CASE-Lab/REACH-Hardware/CAD/InventorProject/Manufacturing/CNC_VacuumCleaner_Adapter.stl

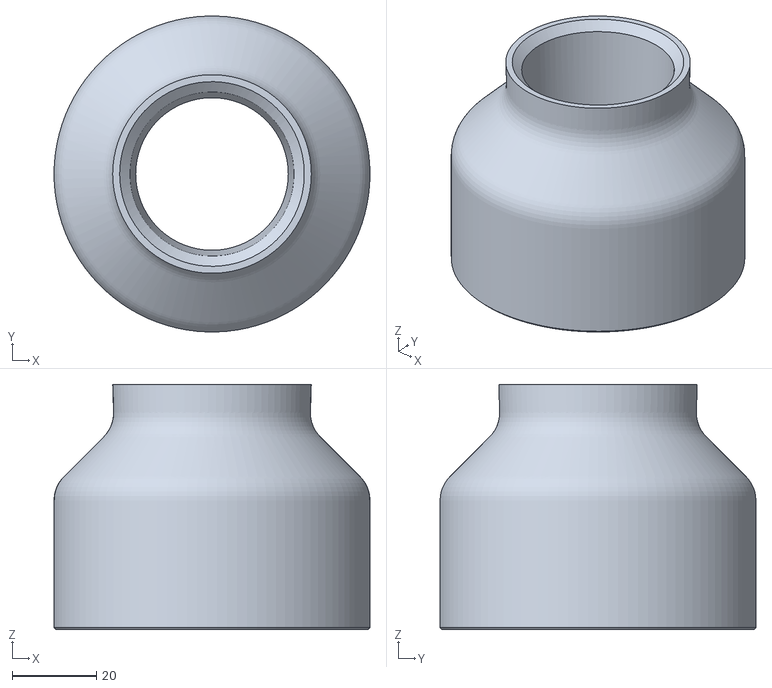
[picture p21: CAD file, 2021-09-06]
CAD/InventorProject/Manufacturing/CNC_VacuumCleaner_Adapter.stl
75.0 x 75.0 x 58.2
