CASE-Lab/REACH-Hardware/CAD/InventorProject/PCB_Outlines/ES_MODULE_OUTLINE.dxf

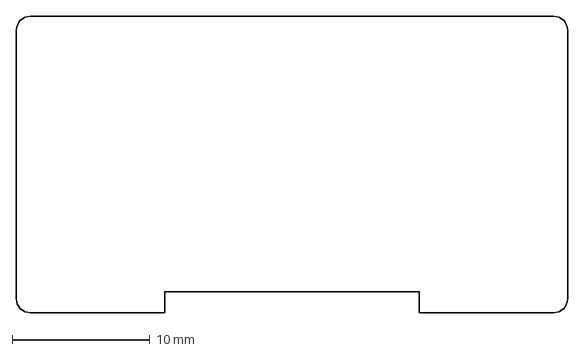
[picture p22: CAD file, 2021-09-06]
CAD/InventorProject/PCB_Outlines/ES_MODULE_OUTLINE.dxf
40.0 x 21.5 mm
