CASE-Lab/REACH-Hardware/CAD/InventorProject/Manufacturing/FrontText.dxf

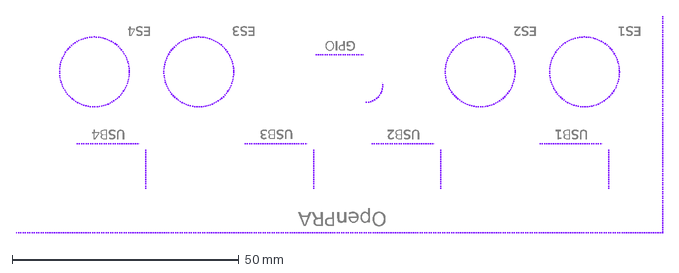
[picture p23: CAD file, 2021-09-06]
CAD/InventorProject/Manufacturing/FrontText.dxf
ES1
ES2
ES4
ES3
USB1
USB2
USB3
USB4
GPIO
OpenPRA
