CASE-Lab/REACH-Hardware/CAD/InventorProject/Manufacturing/UnicornPaneler/BackText.dxf

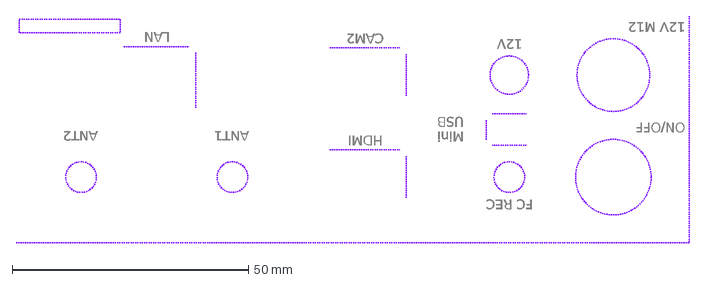
[picture p24: CAD file, 2021-09-06]
CAD/InventorProject/Manufacturing/UnicornPaneler/BackText.dxf
HDMI
CAM2
LAN
ANT1
12V
ANT2
Mini USB
FC REC
ON/OFF
12V M12
