CASE-Lab/REACH-Hardware/CAD/InventorProject/PCB_Outlines/FP_USB_OUTLINE.dxf

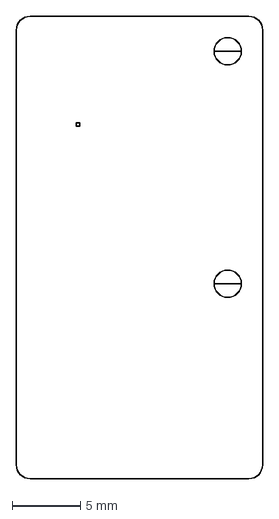
[picture p25: CAD file, 2021-09-06]
CAD/InventorProject/PCB_Outlines/FP_USB_OUTLINE.dxf
18.0 x 33.8 mm
