CASE-Lab/REACH-Hardware/CAD/InventorProject/Manufacturing/BottomTextThin.dxf

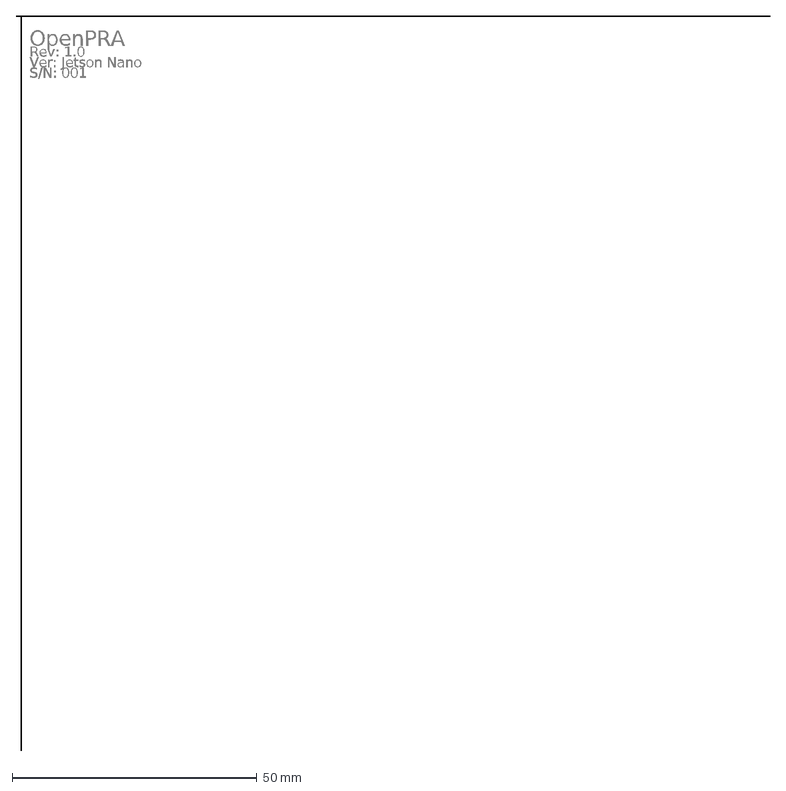
[picture p26: CAD file, 2021-09-06]
CAD/InventorProject/Manufacturing/BottomTextThin.dxf
OpenPRA Rev: 1.0 Ver: Jetson Nano S/N: 001
