CASE-Lab/REACH-Hardware/CAD/InventorProject/PCB_Outlines/FP_PCB_OUTLINE.dxf

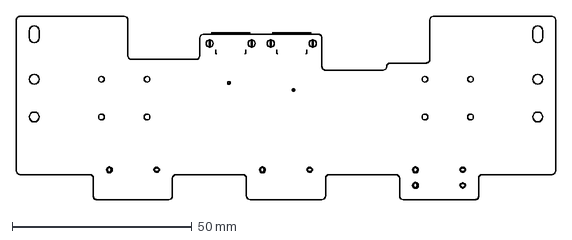
[picture p27: CAD file, 2021-09-06]
CAD/InventorProject/PCB_Outlines/FP_PCB_OUTLINE.dxf
150.0 x 51.0 mm
