CASE-Lab/REACH-Hardware/CAD/InventorProject/Manufacturing/Camera_Con_Spacer.stl

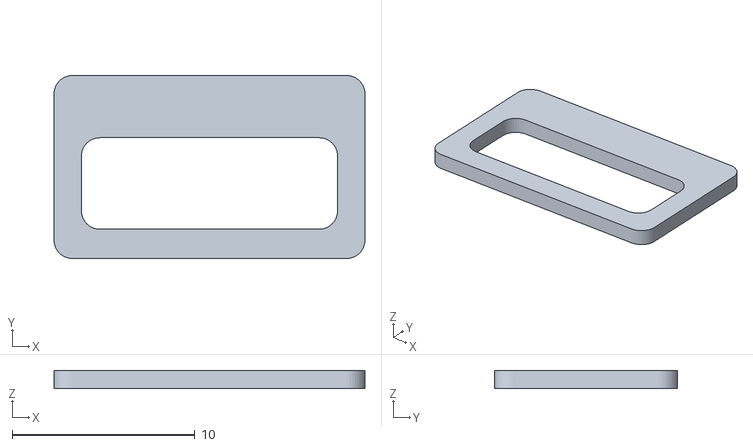
[picture p28: CAD file, 2021-09-06]
CAD/InventorProject/Manufacturing/Camera_Con_Spacer.stl
17.0 x 10.0 x 1.00
