CASE-Lab/REACH-Hardware/CAD/InventorProject/Manufacturing/UnicornPaneler/EngravingBackJig.dxf

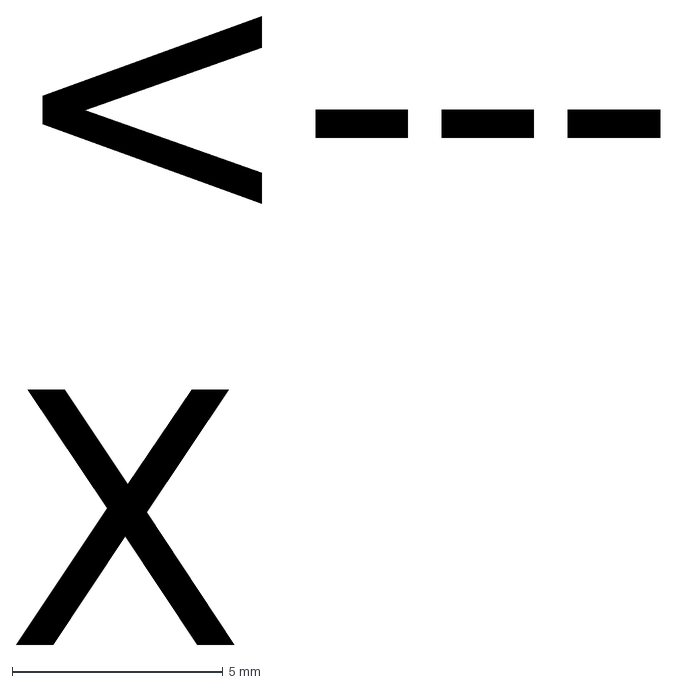
[picture p29: CAD file, 2021-09-06]
CAD/InventorProject/Manufacturing/UnicornPaneler/EngravingBackJig.dxf
<--- X
