CASE-Lab/REACH-Hardware/CAD/InventorProject/Manufacturing/UnicornPaneler/FrontText_V3_LOGO.dxf

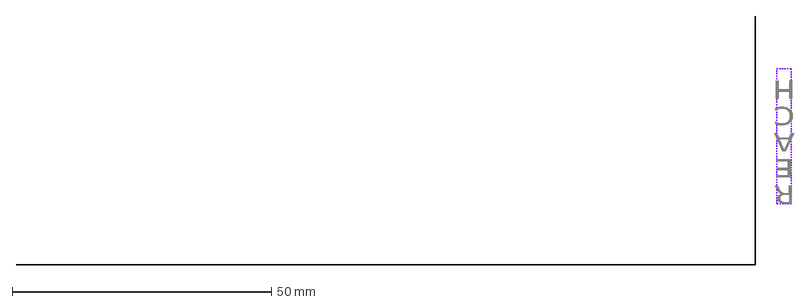
[picture p30: CAD file, 2021-09-06]
CAD/InventorProject/Manufacturing/UnicornPaneler/FrontText_V3_LOGO.dxf
R E A C H
