CASE-Lab/REACH-Hardware/CAD/InventorProject/Manufacturing/UnicornPaneler/BottomText.dxf

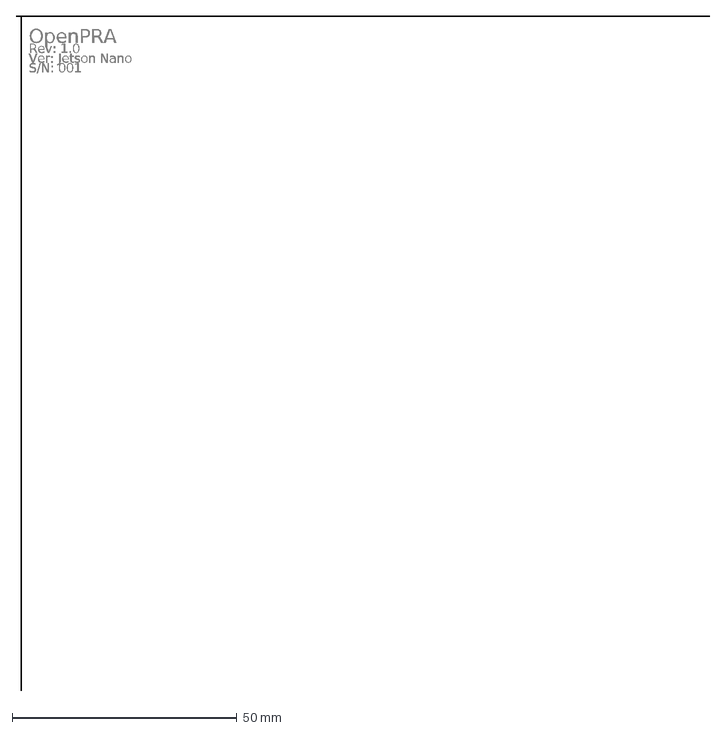
[picture p31: CAD file, 2021-09-06]
CAD/InventorProject/Manufacturing/UnicornPaneler/BottomText.dxf
OpenPRA Rev: 1.0 Ver: Jetson Nano S/N: 001
