CASE-Lab/REACH-Hardware/CAD/InventorProject/Manufacturing/test.dxf

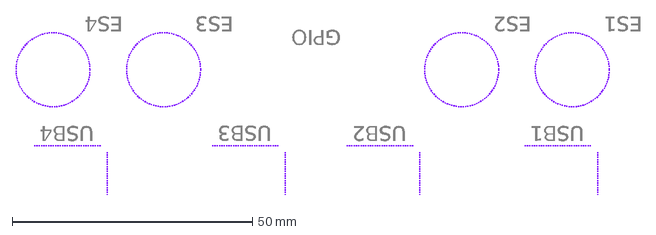
[picture p32: CAD file, 2021-09-06]
CAD/InventorProject/Manufacturing/test.dxf
ES1
ES2
ES4
ES3
USB1
USB2
USB3
USB4
GPIO
