CASE-Lab/REACH-Hardware/CAD/InventorProject/Manufacturing/Connector_Stop.stl

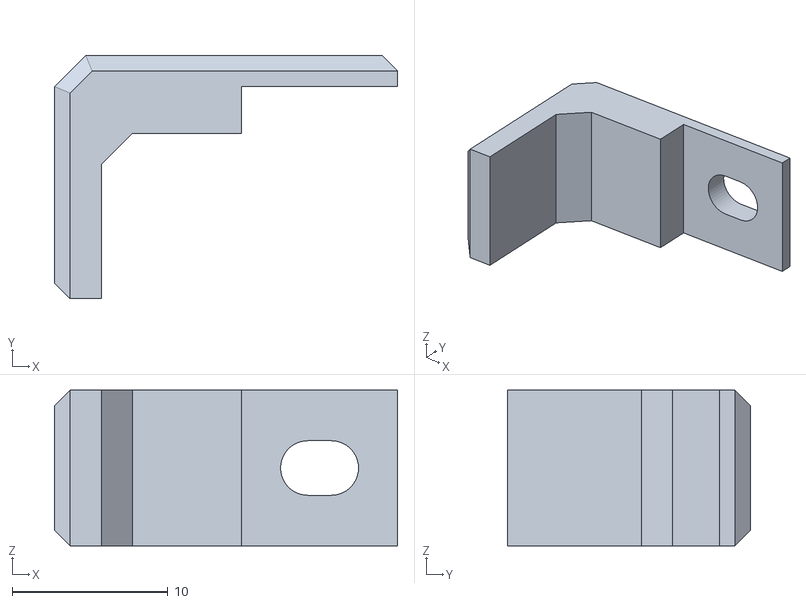
[picture p33: CAD file, 2021-09-06]
CAD/InventorProject/Manufacturing/Connector_Stop.stl
22.0 x 15.6 x 10.0
