CASE-Lab/REACH-Hardware/CAD/InventorProject/Manufacturing/TOP_Marking_ACU.dxf

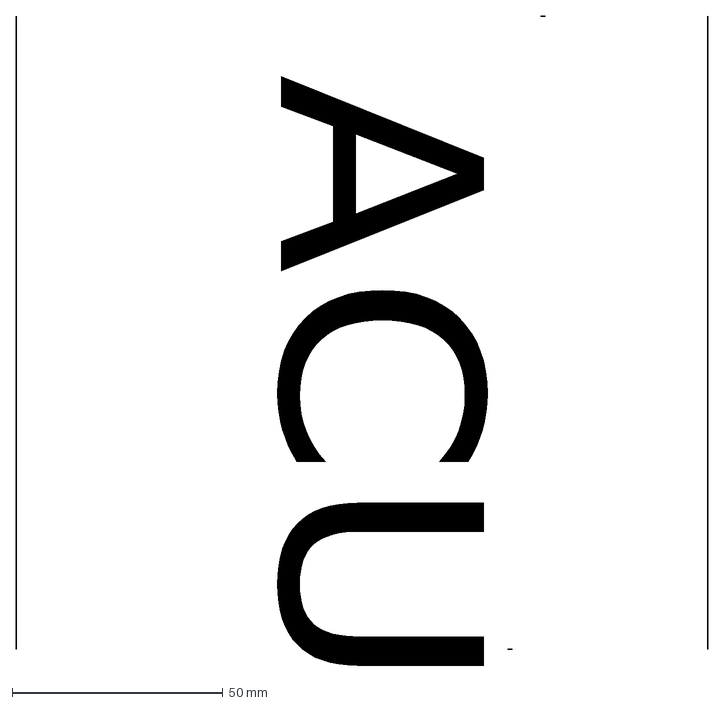
[picture p34: CAD file, 2021-09-06]
CAD/InventorProject/Manufacturing/TOP_Marking_ACU.dxf
ACU
