CASE-Lab/REACH-Hardware/CAD/InventorProject/Manufacturing/UnicornPaneler/BottomText_V2_Xavier_WaveRunner.dxf

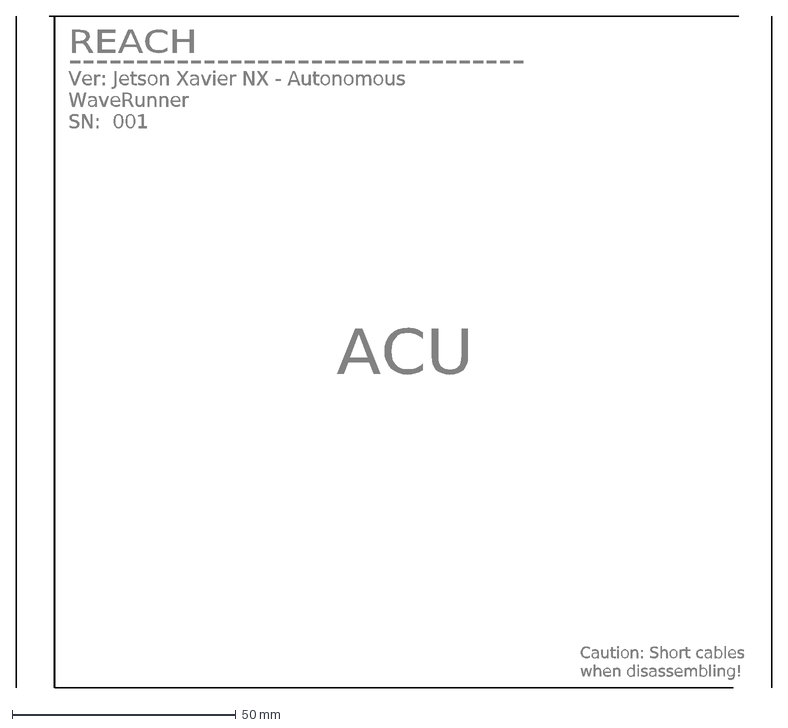
[picture p35: CAD file, 2021-09-06]
CAD/InventorProject/Manufacturing/UnicornPaneler/BottomText_V2_Xavier_WaveRunner.dxf
Ver: Jetson Xavier NX - Autonomous WaveRunner SN: 001
Caution: Short cables when disassembling!
REACH ----------------------------------
ACU
