CASE-Lab/REACH-Hardware/CAD/InventorProject/Manufacturing/AcrylicPlateForFixturePlate.ipt.dxf

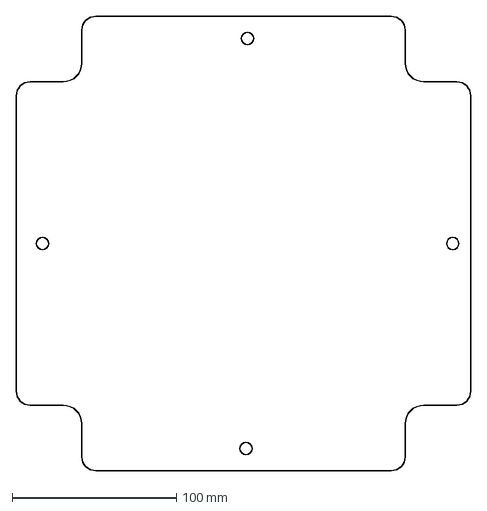
[picture p36: CAD file, 2021-09-06]
CAD/InventorProject/Manufacturing/AcrylicPlateForFixturePlate.ipt.dxf
277.0 x 277.0 mm
