CASE-Lab/REACH-Hardware/CAD/InventorProject/Manufacturing/UnicornPaneler/FrontText_V2.dxf

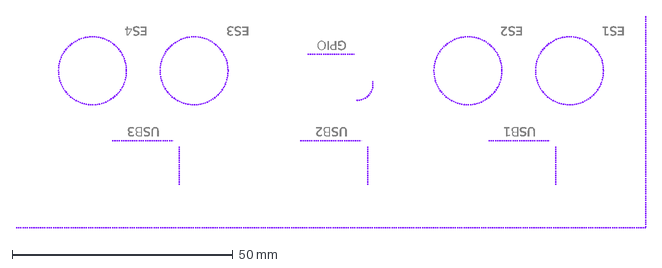
[picture p37: CAD file, 2021-09-06]
CAD/InventorProject/Manufacturing/UnicornPaneler/FrontText_V2.dxf
ES1
ES2
ES4
ES3
USB1
USB2
USB3
GPIO
