CASE-Lab/REACH-Hardware/CAD/InventorProject/Manufacturing/UnicornPaneler/BottomText_V2_Xavier_Standard.dxf

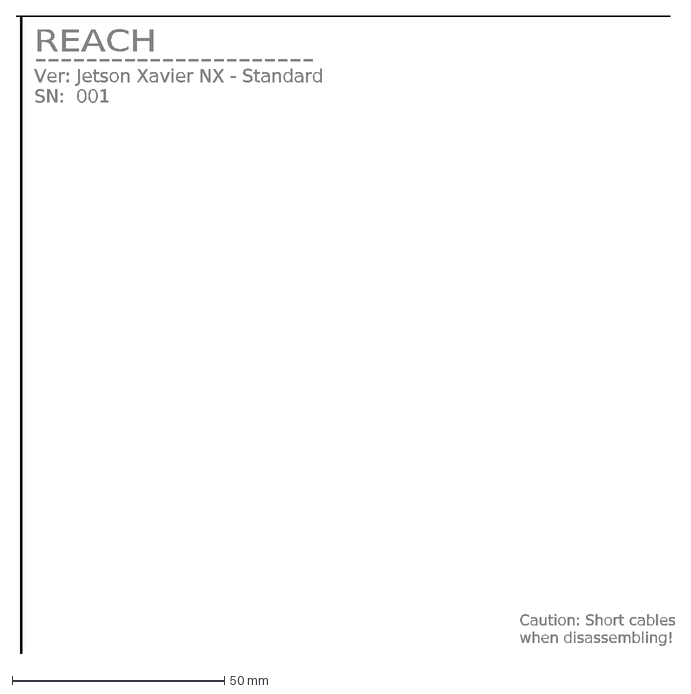
[picture p38: CAD file, 2021-09-06]
CAD/InventorProject/Manufacturing/UnicornPaneler/BottomText_V2_Xavier_Standard.dxf
Ver: Jetson Xavier NX - Standard SN: 001
Caution: Short cables when disassembling!
REACH ----------------------
