CASE-Lab/REACH-Hardware/CAD/InventorProject/Manufacturing/ModuleBracket_Slot_V2.stl

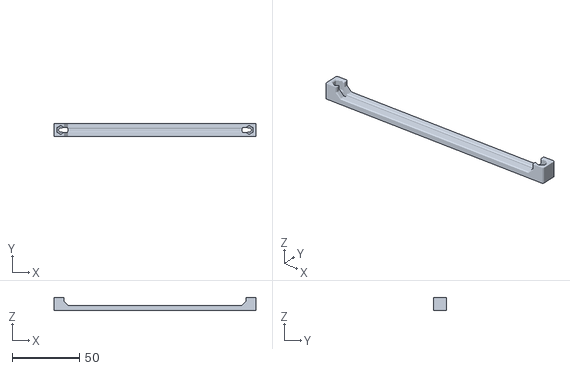
[picture p39: CAD file, 2021-09-06]
CAD/InventorProject/Manufacturing/ModuleBracket_Slot_V2.stl
150.0 x 10.0 x 10.0
